JonathanThing/Arduino-Tetris/Pictures/Back PCB.jpg

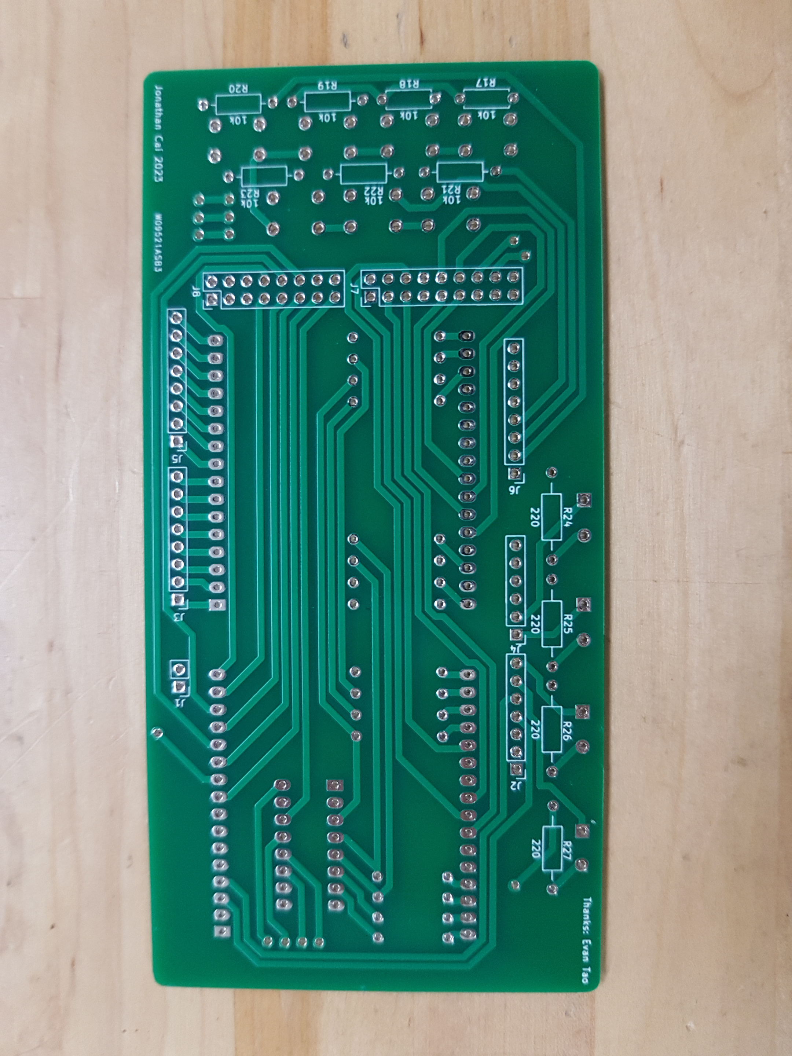
Pictures/Back PCB.jpg
