JonathanThing/Arduino-Tetris/Code/TETRIS/TetrisMusic.cpp

#include "MenuMusic.h"
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
MusicTrack tracksTetrisMusic[] = {
  { 9, freq0, time0, 444 },
  { 8, freq1, time1, 477 },
  { 7, freq2, time2, 431 },
  { 6, freq3, time3, 303 }
};
