JonathanThing/Arduino-Tetris/Code/TETRIS/MenuMusic.cpp

#include "MenuMusic.h"

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
 146, 0, 73, 0, 146, 0, 73, 0, 73, 0, 146, 0, 73, 0, 146, 0, 73, 0, 73, 0, 146, 0, 73, 0, 146, 0, 73, 0, 73, 0, 146, 0, 82, 0, 164, 0, 82, 0, 82, 0, 164, 0, 82, 0, 164, 0, 82, 0, 82, 0, 164, 0, 77, 0, 155, 0, 77, 0, 77, 0, 155, 0, 77, 0, 155, 0, 77, 0, 77, 0, 155, 0, 73, 0, 146, 0, 73, 0, 73, 0, 146, 0, 73, 0, 146, 0, 73, 0, 73, 0, 146, 0, 73, 0, 146, 0, 73, 0, 73, 0, 146, 0, 73, 0, 146, 0, 73, 0, 220, 0, 184, 0, 164, 0, 164, 0, 164, 0, 123, 0, 123, 0, 164, 0, 164, 0, 164, 0, 123, 0, 123, 0, 164, 0, 0 };
const uint32_t time11[] PROGMEM = { 0, 99, 200, 294, 300, 394, 400, 499, 600, 699, 800, 899, 1000, 1094, 1100, 1194, 1200, 1299, 1400, 1499, 1600, 1699, 1800, 1894, 1900, 1994, 2000, 2099, 2200, 2299, 2400, 2499, 2600, 2694, 2700, 2794, 2800, 2899, 3000, 3099, 3200, 3299, 3400, 3494, 3500, 3594, 3600, 3699, 3800, 3899, 4000, 4099, 4200, 4294, 4300, 4394, 4400, 4499, 4600, 4699, 4800, 4899, 5000, 5094, 5100, 5194, 5200, 5299, 5400, 5499, 5600, 5699, 5800, 5894, 5900, 5994, 6000, 6099, 6200, 6299, 6400, 6499, 6600, 6694, 6700, 6794, 6800, 6899, 7000, 7099, 7200, 7299, 7400, 7494, 7500, 7594, 7600, 7699, 7800, 7899, 8000, 8099, 8200, 8294, 8300, 8394, 8400, 8499, 8600, 8699, 8800, 8899, 9000, 9094, 9100, 9194, 9200, 9299, 9400, 9499, 9600, 9699, 9800, 9894, 9900, 9994, 10000, 10099, 10200, 10299, 10400, 10499, 10600, 10694, 10700, 10794, 10800, 10899, 11000, 11099, 11200, 11299, 11400, 11494, 11500, 11594, 11600, 11699, 11800, 11899, 12000, 12099, 12200, 12294, 12300, 12394, 12400, 12499, 12600, 12699, 12800, 12899, 13000, 13094, 13100, 13194, 13200, 13299, 13400, 13499, 13600, 13699, 13800, 13894, 13900, 13994, 14000, 14099, 14200, 14299, 14400, 14499, 14600, 14694, 14700, 14794, 14800, 14899, 15000, 15099, 15200, 15299, 15400, 15494, 15500, 15594, 15600, 15699, 15800, 15899, 16000, 16099, 16200, 16294, 16300, 16394, 16400, 16499, 16600, 16699, 16800, 16899, 17000, 17094, 17100, 17194, 17200, 17299, 17400, 17499, 17600, 17699, 17800, 17894, 17900, 17994, 18000, 18099, 18200, 18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
9699, 69800, 69894, 69900, 69994, 70000, 70099, 70200, 70299, 70400, 70499, 70600, 70694, 70700, 70794, 70800, 70899, 71000, 71099, 71200, 71299, 71400, 71494, 71500, 71594, 71600, 71699, 71800, 71899, 72000, 72099, 72100 };
const uint16_t freq21[] PROGMEM = { 73, 0, 73, 0, 73, 0, 73, 0, 73, 0, 73, 0, 73, 0, 73, 0, 73, 0, 73, 0, 73, 0, 73, 0, 73, 0, 73, 0, 73, 0, 73, 0, 73, 0, 73, 0, 73, 0, 73, 0, 73, 0, 73, 0, 73, 0, 73, 0, 73, 0, 73, 0, 73, 0, 73, 0, 73, 0, 73, 0, 73, 0, 73, 0, 73, 0, 73, 0, 73, 0, 73, 0, 73, 0, 73, 0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
const uint32_t time21[] PROGMEM = { 0, 99, 200, 299, 300, 399, 400, 499, 600, 699, 800, 899, 1000, 1099, 1100, 1199, 1200, 1299, 1400, 1499, 1600, 1699, 1800, 1899, 1900, 1999, 2000, 2099, 2200, 2299, 2400, 2499, 2600, 2699, 2700, 2799, 2800, 2899, 3000, 3099, 3200, 3299, 3400, 3499, 3500, 3599, 3600, 3699, 3800, 3899, 4000, 4099, 4200, 4299, 4300, 4399, 4400, 4499, 4600, 4699, 4800, 4899, 5000, 5099, 5100, 5199, 5200, 5299, 5400, 5499, 5600, 5699, 5800, 5899, 5900, 5999, 6000, 6099, 6200, 6299, 6400, 6499, 6600, 6699, 6700, 6799, 6800, 6899, 7000, 7099, 7200, 7299, 7400, 7499, 7500, 7599, 7600, 7699, 7800, 7899, 8000, 8099, 8200, 8299, 8300, 8399, 8400, 8499, 8600, 8699, 8800, 8899, 9000, 9099, 9100, 9199, 9200, 9299, 9400, 9499, 9600, 9699, 9800, 9899, 9900, 9999, 10000, 10099, 10200, 10299, 10400, 10499, 10600, 10699, 10700, 10799, 10800, 10899, 11000, 11099, 11200, 11299, 11400, 11499, 11500, 11599, 11600, 11699, 11800, 11899, 12000, 12099, 12200, 12299, 12300, 12399, 12400, 12499, 12600, 12699, 12800, 12899, 13000, 13099, 13100, 13199, 13200, 13299, 13400, 13499, 13600, 13699, 13800, 13899, 13900, 13999, 14000, 14099, 14200, 14299, 14400, 14499, 14600, 14699, 14700, 14799, 14800, 14899, 15000, 15099, 15200, 15299, 15400, 15499, 15500, 15599, 15600, 15699, 15800, 15899, 16000, 16099, 16200, 16299, 16300, 16399, 16400, 16499, 16600, 16699, 16800, 16899, 17000, 17099, 17100, 17199, 17200, 17299, 17400, 17499, 17600, 17699, 17800, 17899, 17900, 17999, 18000, 18099, 18200, 18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
, 61900, 61994, 62000, 62099, 62200, 62299, 62400, 62499, 62600, 62694, 62700, 62794, 62800, 62899, 63000, 63099, 63200, 63299, 63400, 63499, 63600, 63699, 63800, 63899, 64000, 64099, 64200, 64294, 64300, 64394, 64400, 64499, 64600, 64699, 65000, 65094, 65100, 65194, 65200, 65299, 65600, 65699, 65800, 65894, 65900, 65994, 66000, 66099, 66200, 66299, 66600, 66694, 66700, 66794, 66800, 66899, 67000, 67099, 67200, 67299, 72100 };

MusicTrack tracksMenuMusic[] = {
  { 9, freq01, time01, 628 },
  { 8, freq11, time11, 904 },
  { 7, freq21, time21, 903 },
  { 6, freq31, time31, 495 }
};
