JonathanThing/Arduino-Tetris/Code/TETRIS/Colour.h

#ifndef COLOUR_H
#define COLOUR_H
#include <Arduino.h>

extern byte COLOUR_MAX_VALUE;

struct Colour {
  byte red;
  byte green;
  byte blue;

  Colour();
  Colour(byte red, byte green, byte blue);
  void printOut();
  void changeRed(int delta);
  void changeGreen(int delta);
  void changeBlue(int delta);
  void changeColour(int redDelta, int greenDelta, int blueDelta);
  byte getColourValue(byte selection);
};

extern const Colour RED;
extern const Colour GREEN;
extern const Colour BLUE;
extern const Colour WHITE;
extern const Colour PURPLE;
extern const Colour YELLOW;
extern const Colour ORANGE;
extern const Colour CYAN;
extern const Colour BLACK;
extern const Colour GREY;

extern const Colour ALL_COLOURS[9];


#endif
